uzzambutt/NorthernStudios-Custom-RP2040-Dev-Board-with-Gyro/src/image_2025-12-04_130047476.png

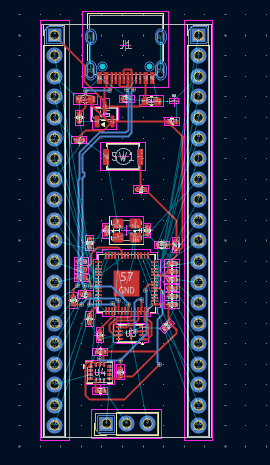
src/image_2025-12-04_130047476.png
